forrana/magnolia-staff/files/STLs/Optional/riser-ring.stl

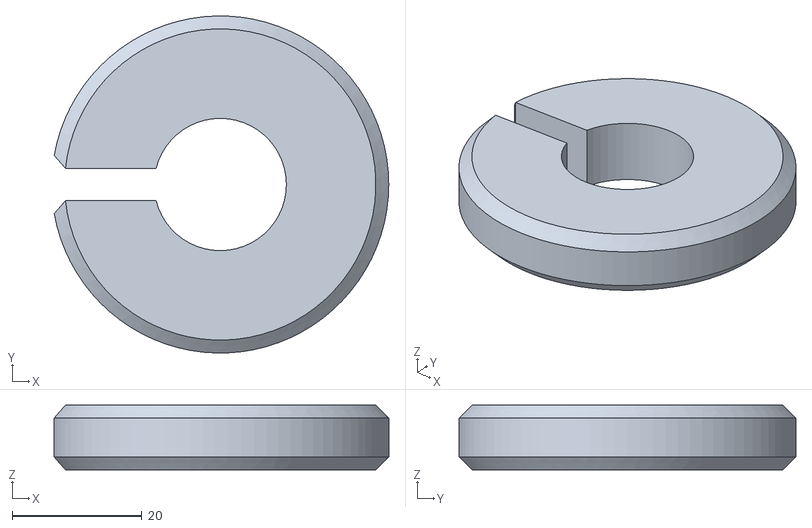
[picture p12: CAD file, 2026-05-13]
files/STLs/Optional/riser-ring.stl
51.6 x 52.0 x 10.0
