forrana/magnolia-staff/files/CAD/STEP/riser-ring-18mm.step

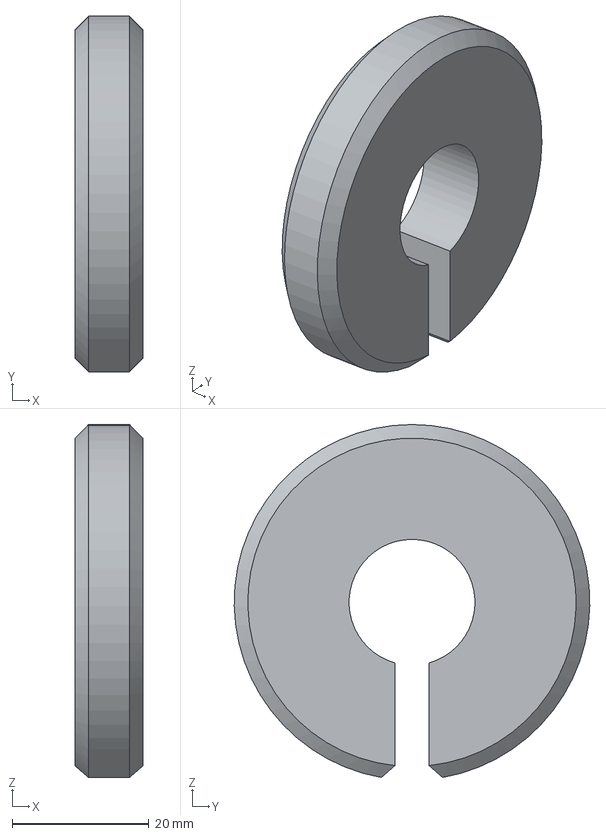
[picture p13: CAD file, 2026-05-13]
files/CAD/STEP/riser-ring-18mm.step
10.0 x 52.0 x 51.6 mm
