forrana/magnolia-staff/files/CAD/FreeCAD/rear-end-18mm.FCStd

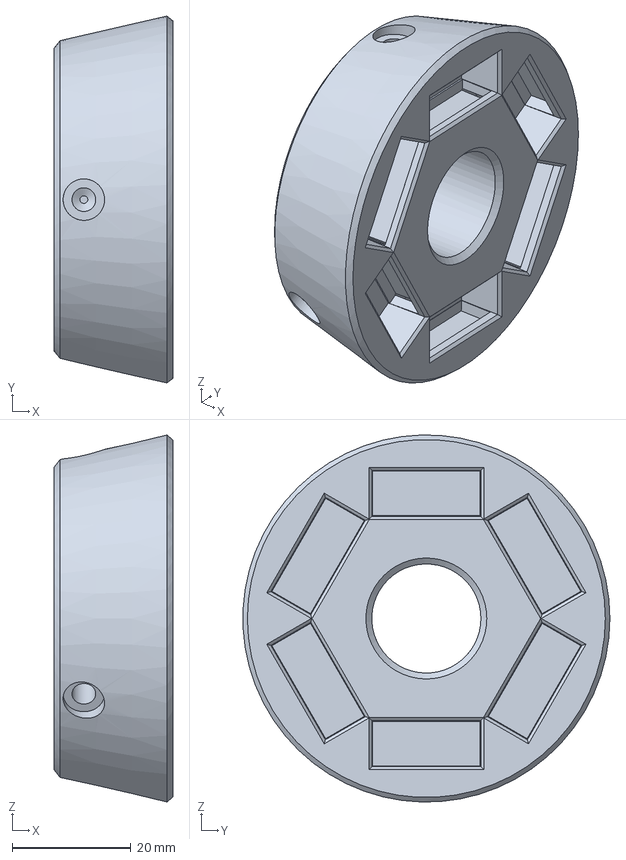
[picture p14: CAD file, 2026-05-13]
files/CAD/FreeCAD/rear-end-18mm.FCStd
20.0 x 61.9 x 61.9 mm
