forrana/magnolia-staff/files/CAD/STEP/front-end-base-18mm.step

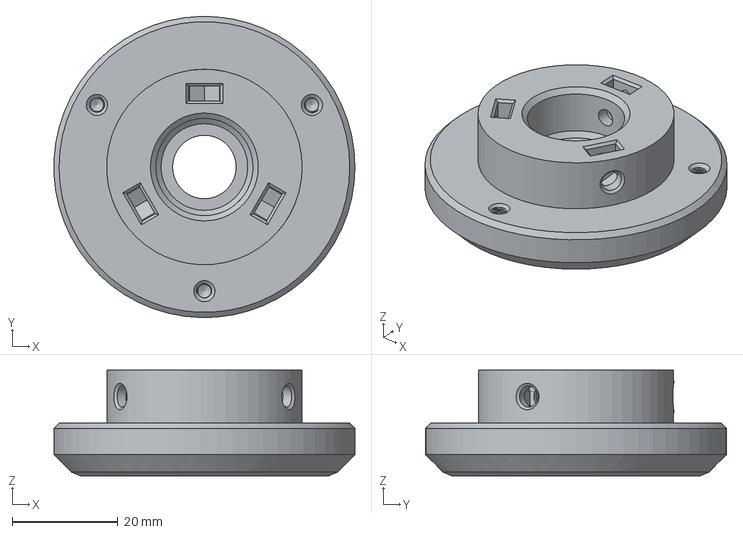
[picture p15: CAD file, 2026-05-05]
files/CAD/STEP/front-end-base-18mm.step
57.0 x 57.0 x 20.0 mm
